CheapMansNode/Cheap-Mans-Node/Pics/3dprinting/3dprinting-02.png

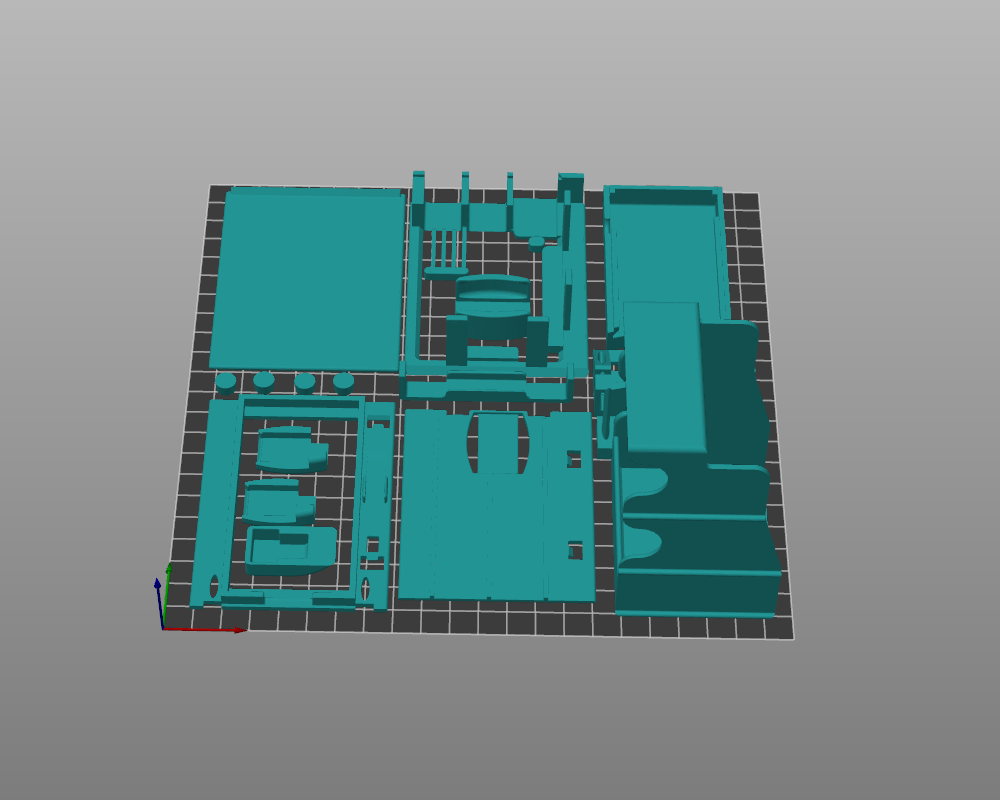
Pics/3dprinting/3dprinting-02.png
