CheapMansNode/Cheap-Mans-Node/Pics/3dprinting/3dprinting-03.png

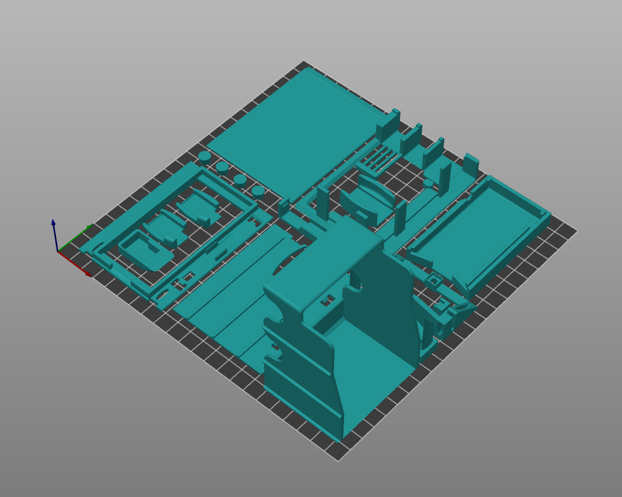
Pics/3dprinting/3dprinting-03.png
