CheapMansNode/Cheap-Mans-Node/Pics/3dprinting/3dprinting-04.png

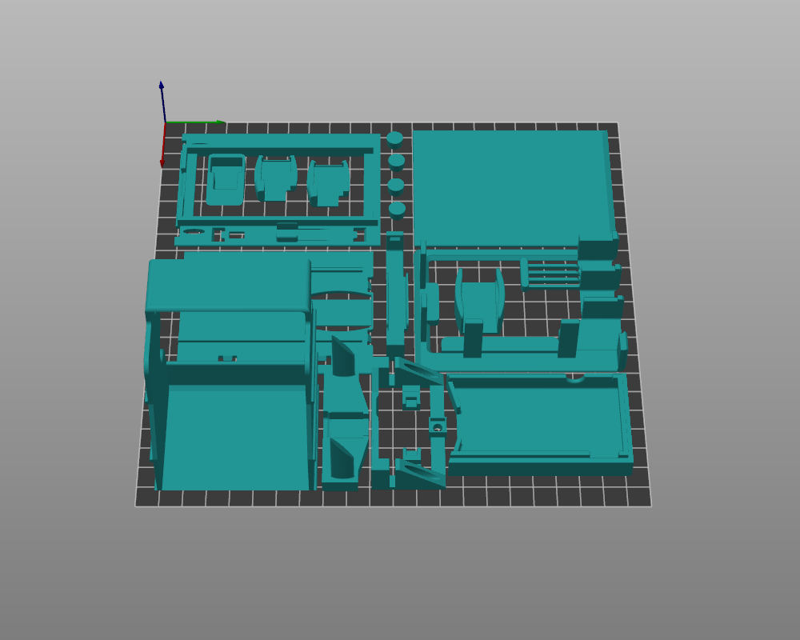
Pics/3dprinting/3dprinting-04.png
