CheapMansNode/Cheap-Mans-Node/Pics/3dprinting/3dprinting-05.png

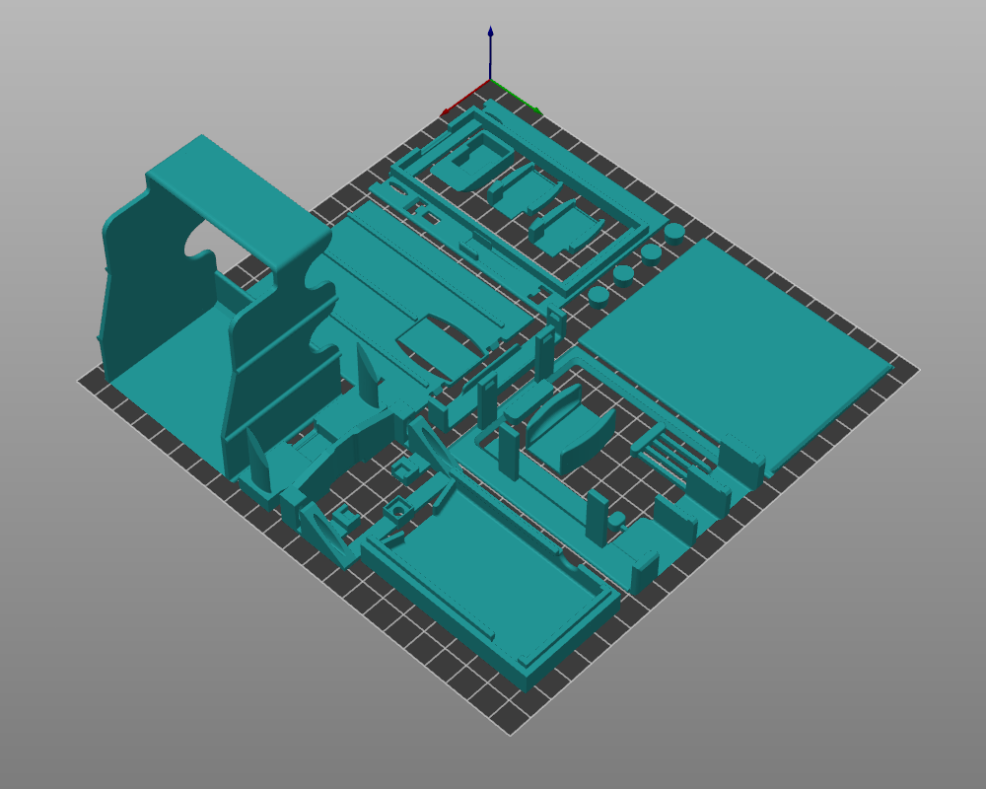
Pics/3dprinting/3dprinting-05.png
