CheapMansNode/Cheap-Mans-Node/Pics/3dprinting/3dprinting-06.png

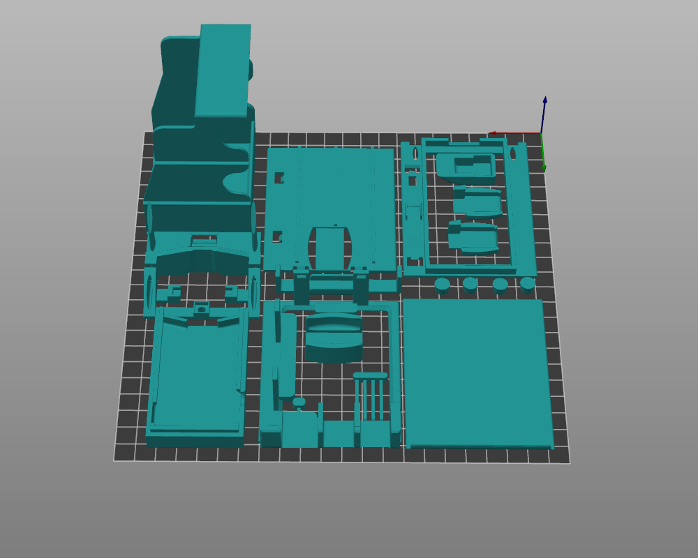
Pics/3dprinting/3dprinting-06.png
