CheapMansNode/Cheap-Mans-Node/Pics/3dprinting/3dprinting-07.png

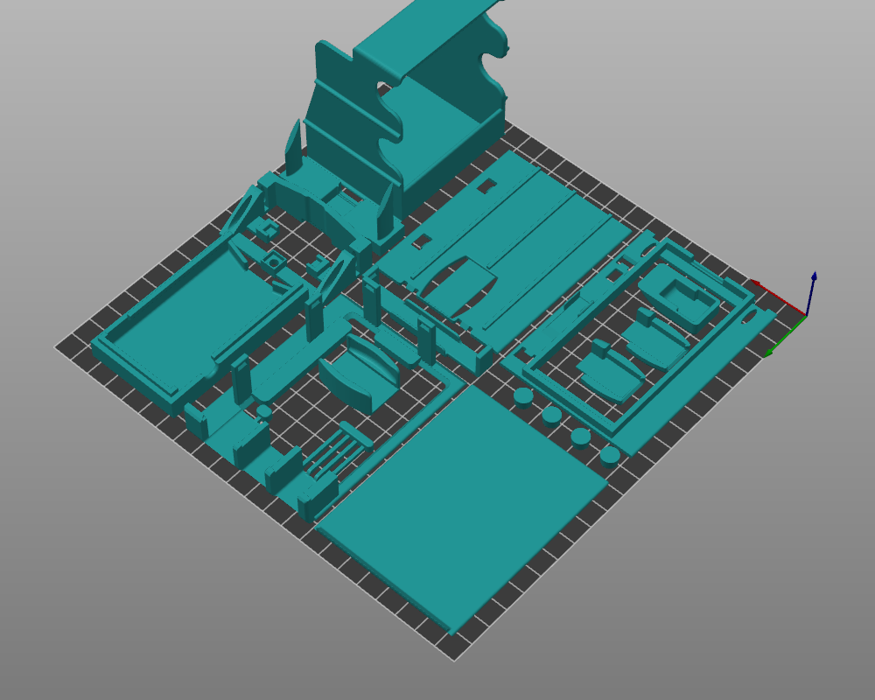
Pics/3dprinting/3dprinting-07.png
