CheapMansNode/Cheap-Mans-Node/Pics/3dprinting/3dprinting-08.png

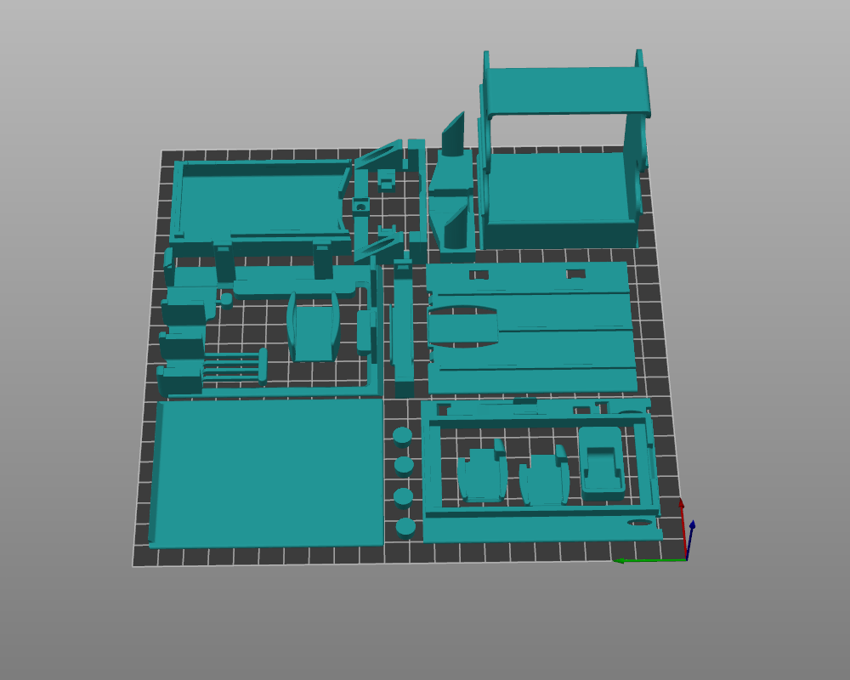
Pics/3dprinting/3dprinting-08.png
