CheapMansNode/Cheap-Mans-Node/Pics/3dprinting/3dprinting-09.png

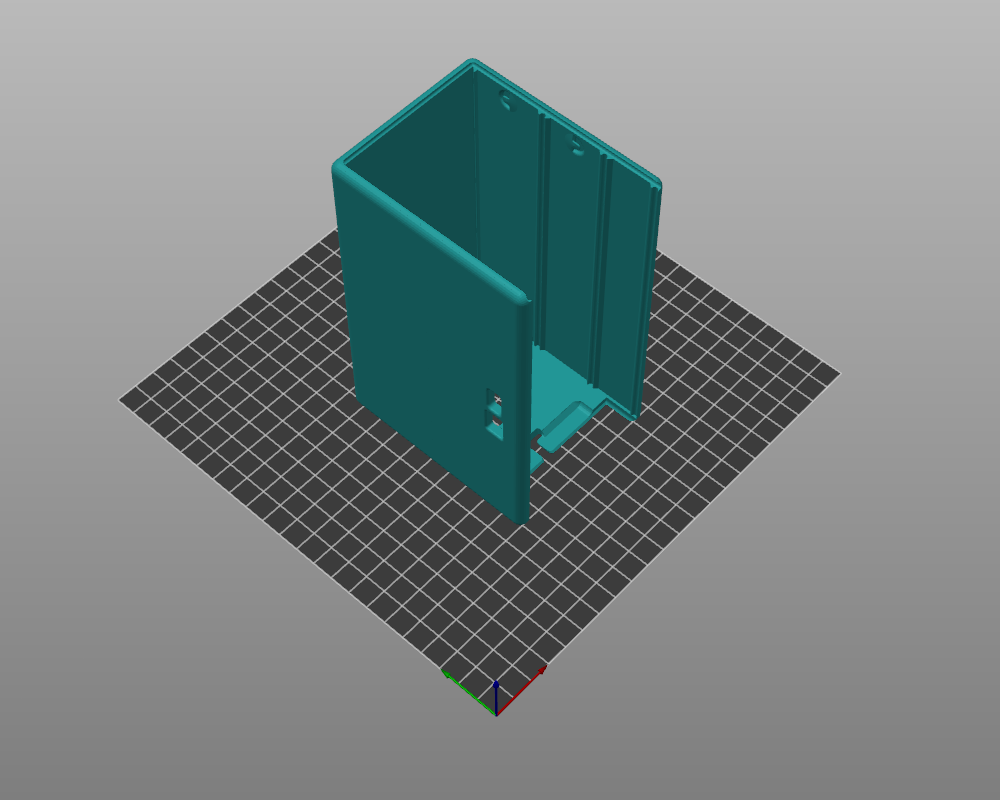
Pics/3dprinting/3dprinting-09.png
