CheapMansNode/Cheap-Mans-Node/Pics/3dprinting/3dprinting-10.png

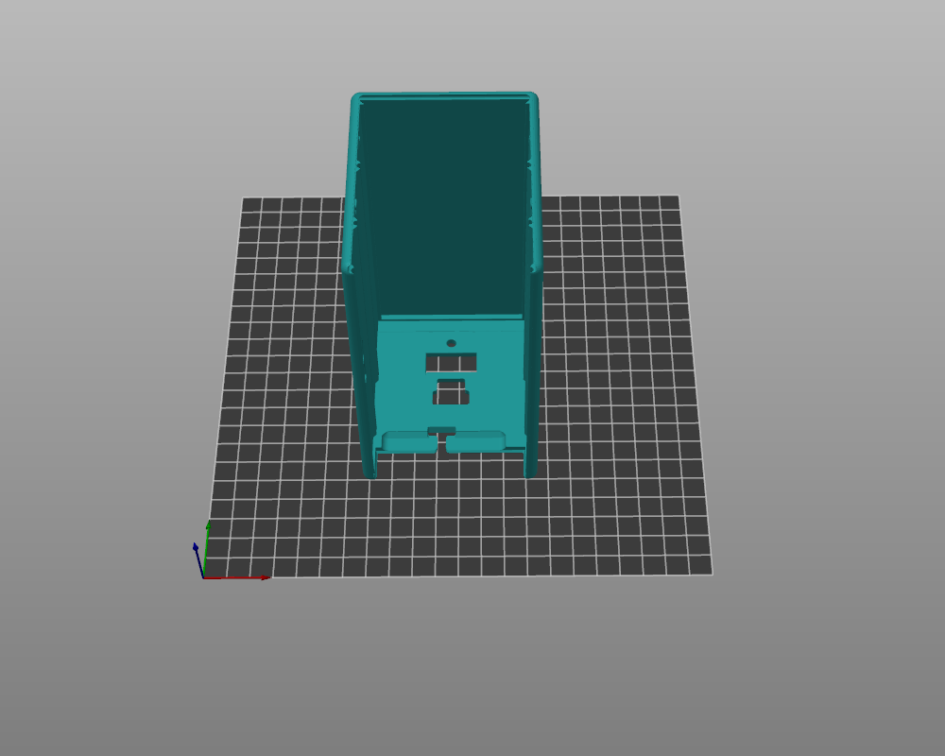
Pics/3dprinting/3dprinting-10.png
