CheapMansNode/Cheap-Mans-Node/Pics/3dprinting/3dprinting-11.png

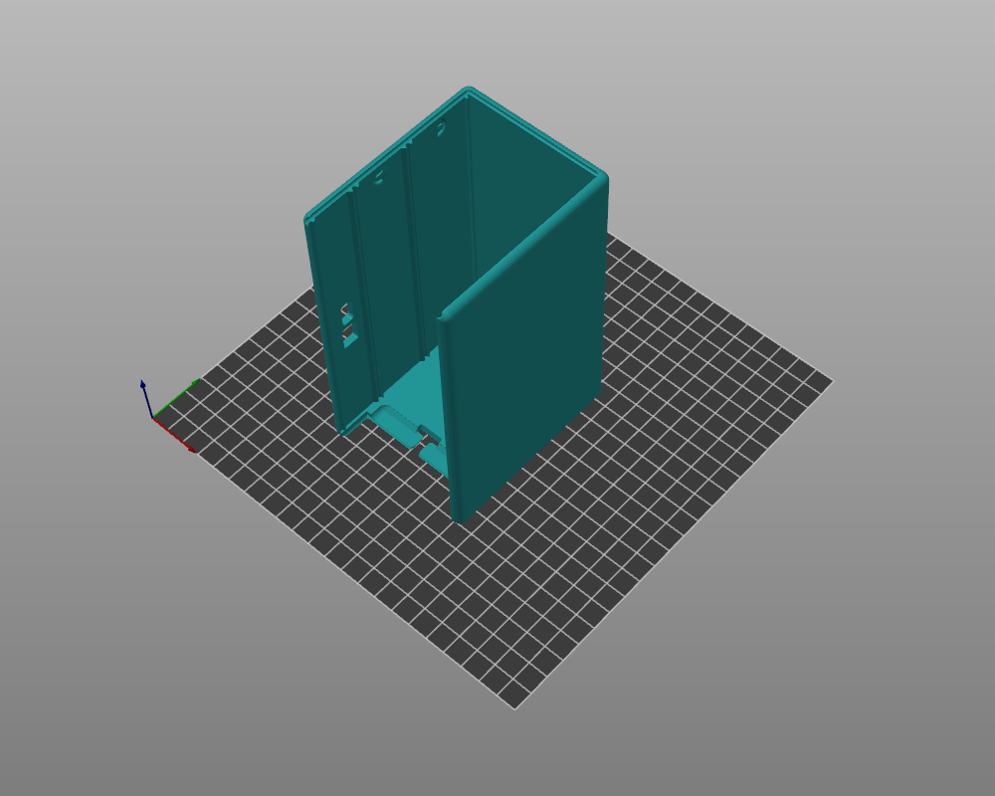
Pics/3dprinting/3dprinting-11.png
