CheapMansNode/Cheap-Mans-Node/Pics/3dprinting/3dprinting-12.png

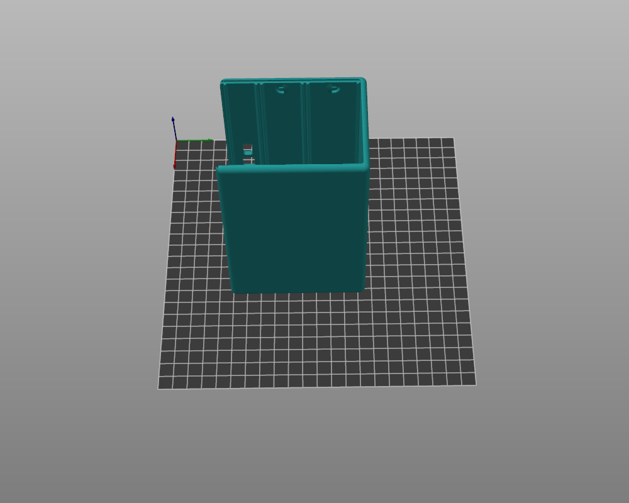
Pics/3dprinting/3dprinting-12.png
