CheapMansNode/Cheap-Mans-Node/Pics/3dprinting/3dprinting-14.png

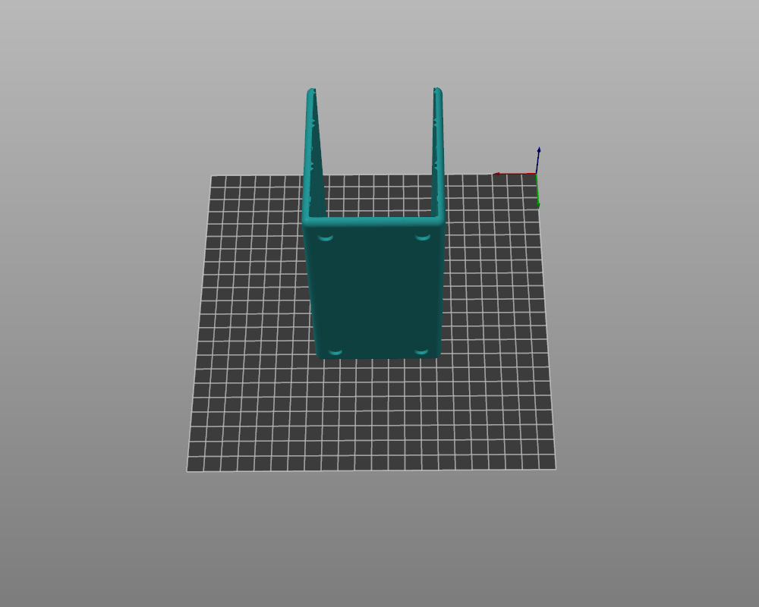
Pics/3dprinting/3dprinting-14.png
