CheapMansNode/Cheap-Mans-Node/Pics/3dprinting/3dprinting-15.png

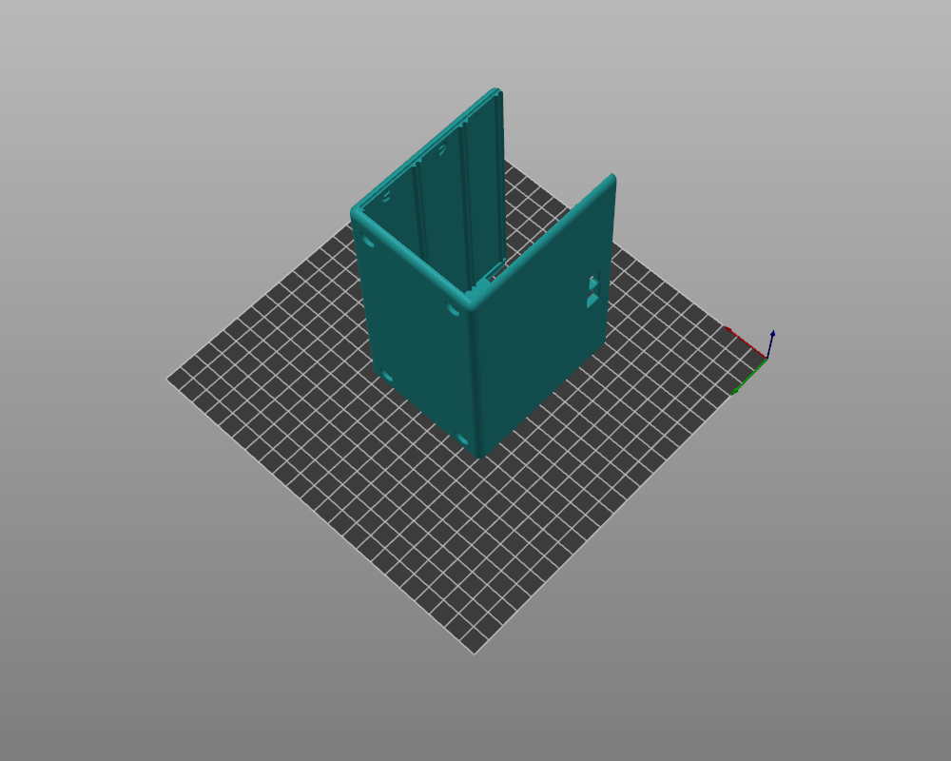
Pics/3dprinting/3dprinting-15.png
