CheapMansNode/Cheap-Mans-Node/Pics/3dprinting/3dprinting-16.png

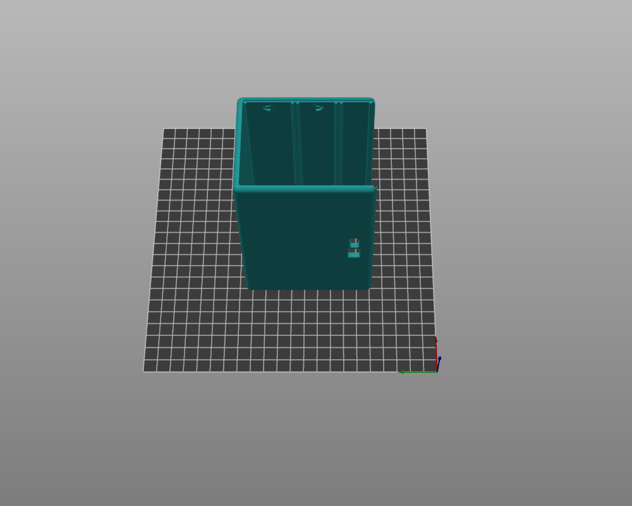
Pics/3dprinting/3dprinting-16.png
