CheapMansNode/Cheap-Mans-Node/Pics/cmn_round_image.jpg

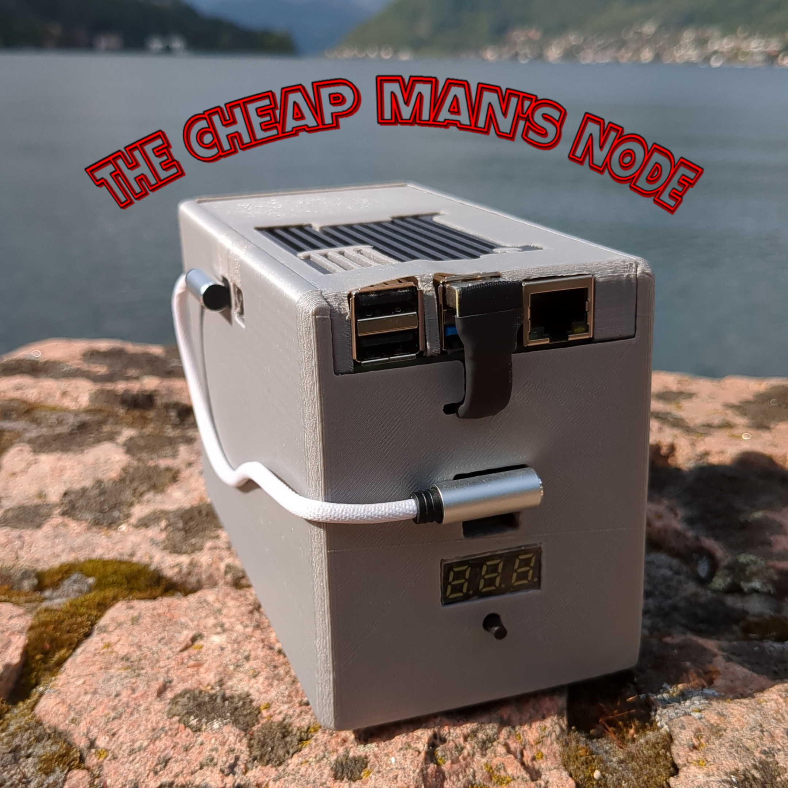
Pics/cmn_round_image.jpg
