CheapMansNode/Cheap-Mans-Node/Pics/gif_pics.gif

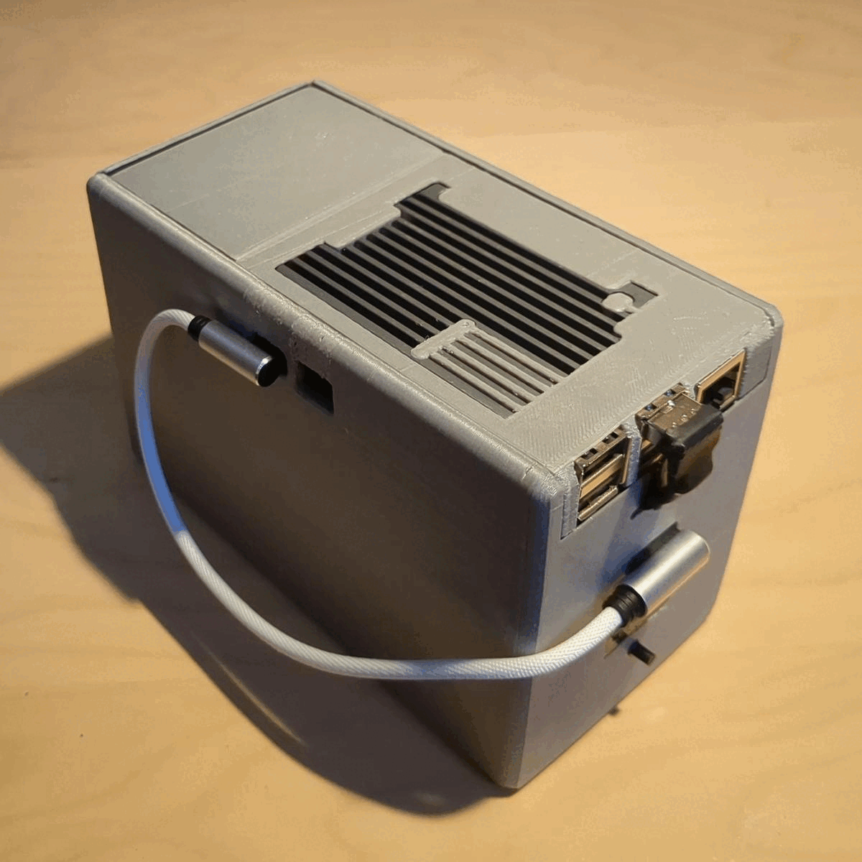
Pics/gif_pics.gif
