CheapMansNode/Cheap-Mans-Node/Pics/gif_render.gif

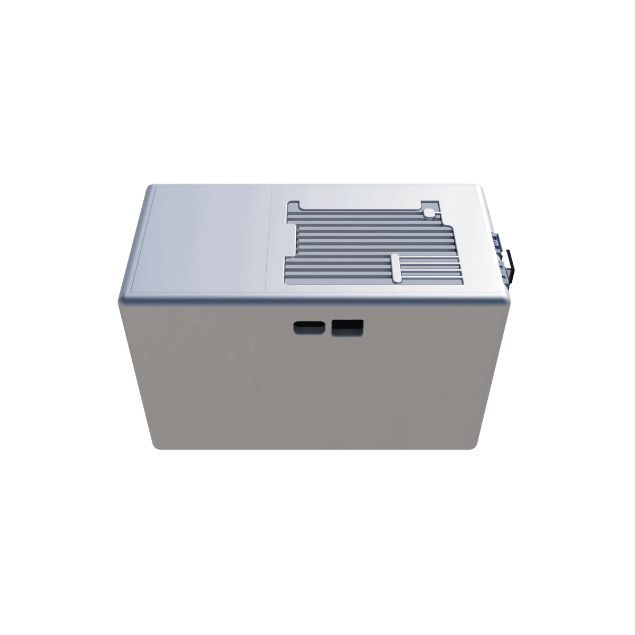
Pics/gif_render.gif
