CheapMansNode/Cheap-Mans-Node/Pics/Render/2.PNG

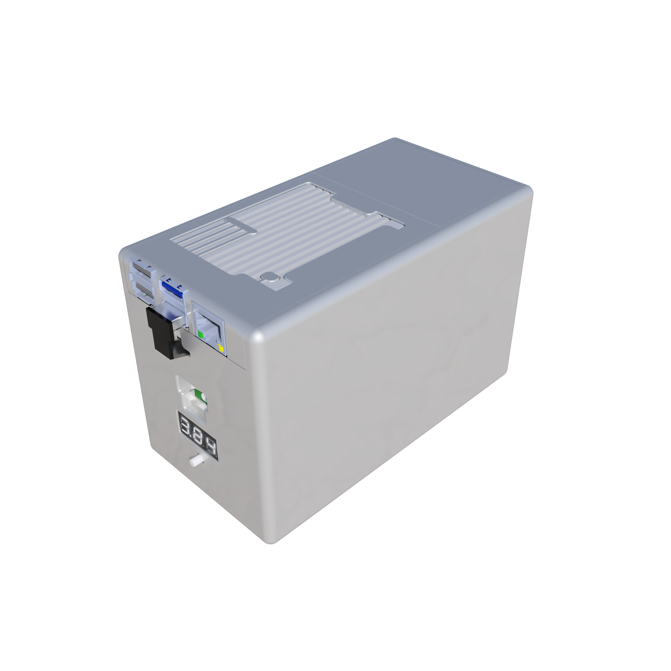
Pics/Render/2.PNG
