CheapMansNode/Cheap-Mans-Node/Pics/Render/3.PNG

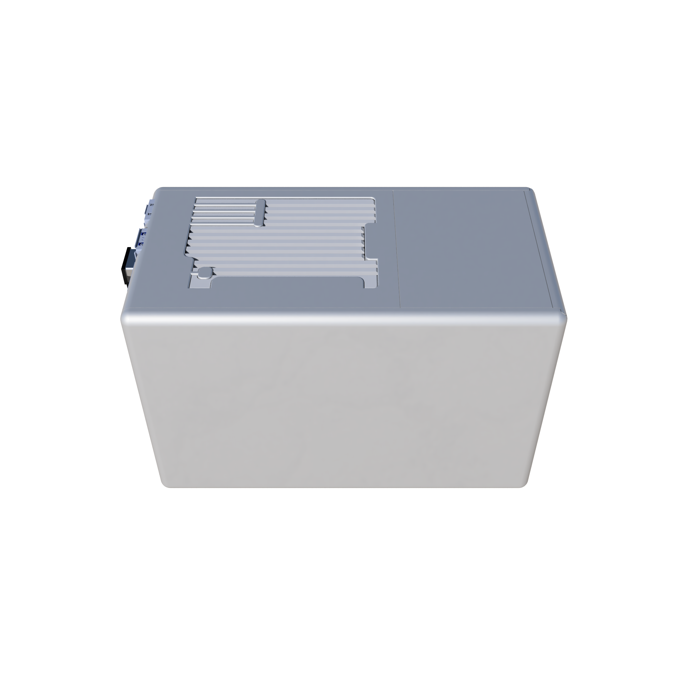
Pics/Render/3.PNG
