CheapMansNode/Cheap-Mans-Node/Pics/Render/4.PNG

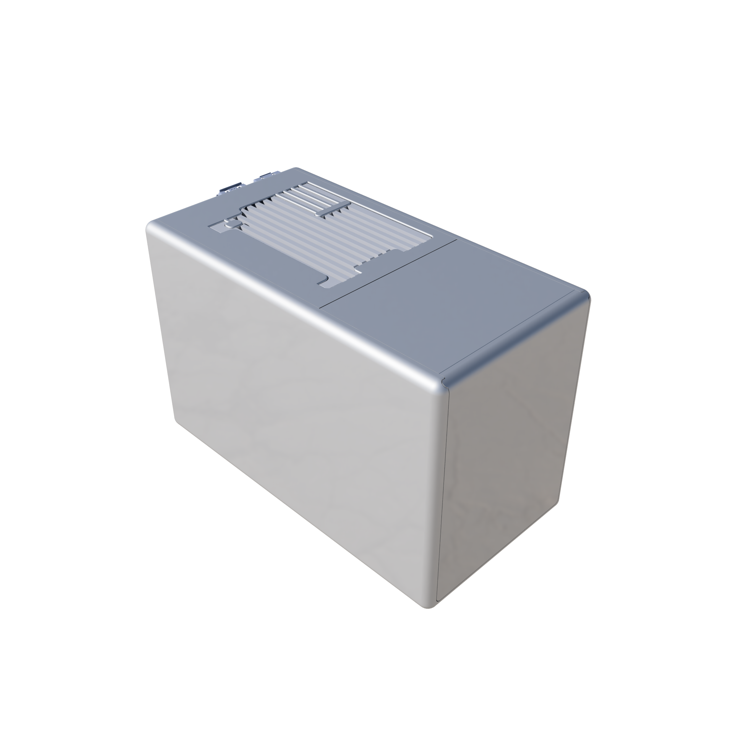
Pics/Render/4.PNG
