CheapMansNode/Cheap-Mans-Node/Pics/Render/5.PNG

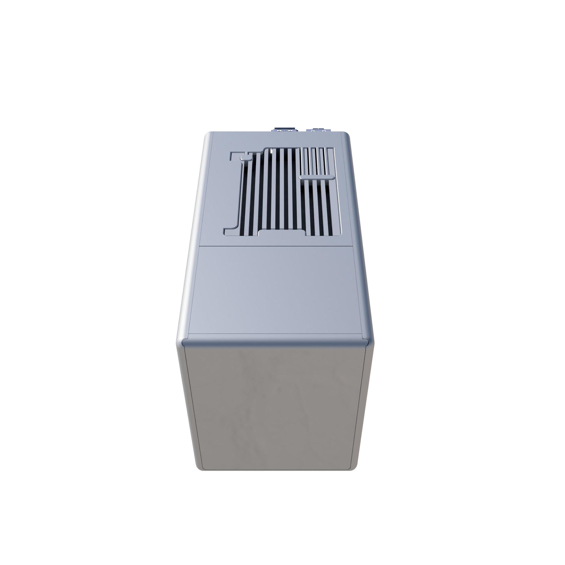
Pics/Render/5.PNG
