CheapMansNode/Cheap-Mans-Node/Pics/Render/6.png

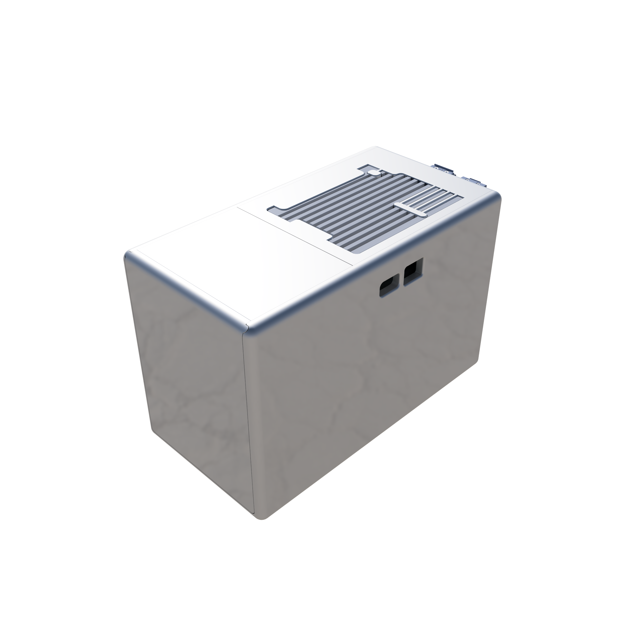
Pics/Render/6.png
