CheapMansNode/Cheap-Mans-Node/Pics/Render/8.png

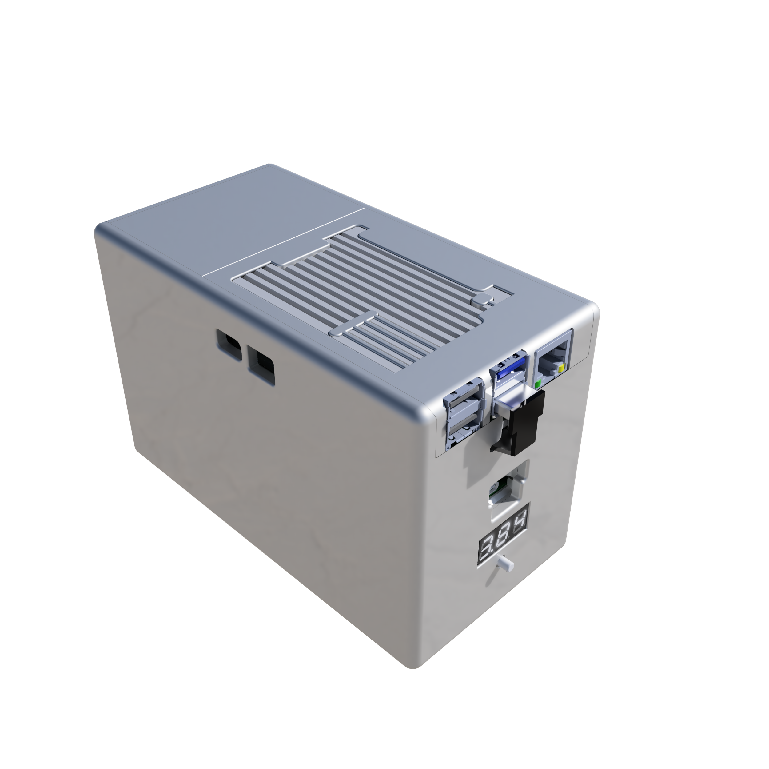
Pics/Render/8.png
