CheapMansNode/Cheap-Mans-Node/Pics/top_a_or_b.jpg

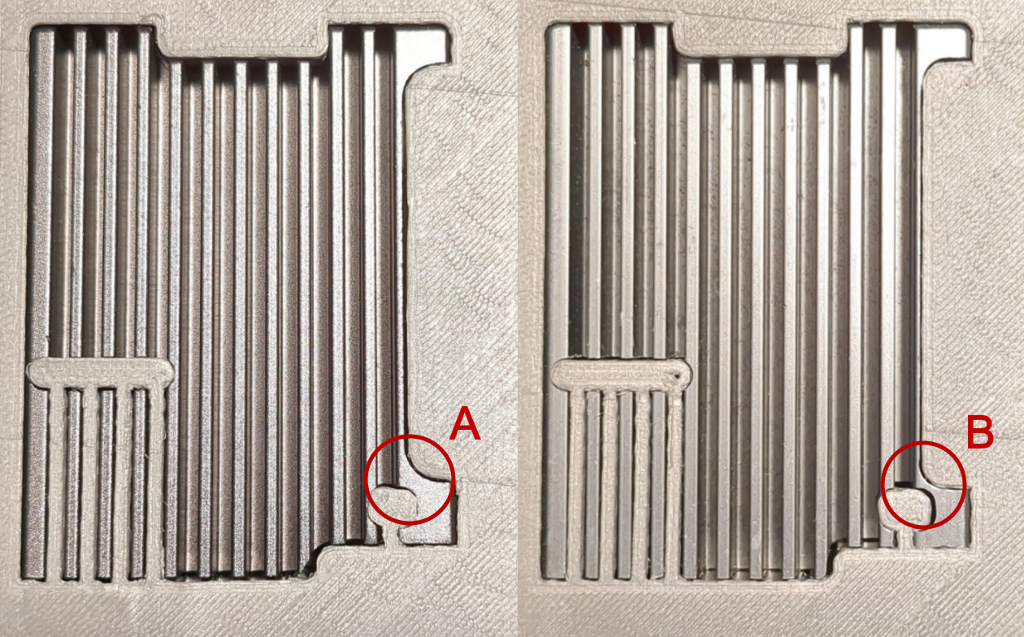
Pics/top_a_or_b.jpg
