CheapMansNode/Cheap-Mans-Node/Pics/3D Printed/1.jpg

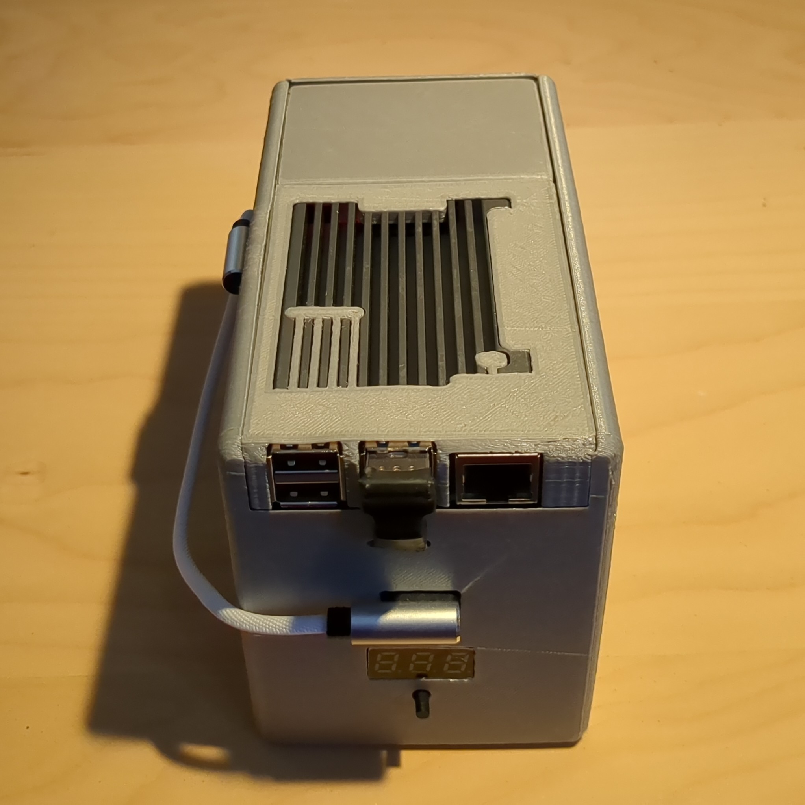
Pics/3D Printed/1.jpg
