CheapMansNode/Cheap-Mans-Node/Pics/3D Printed/2.jpg

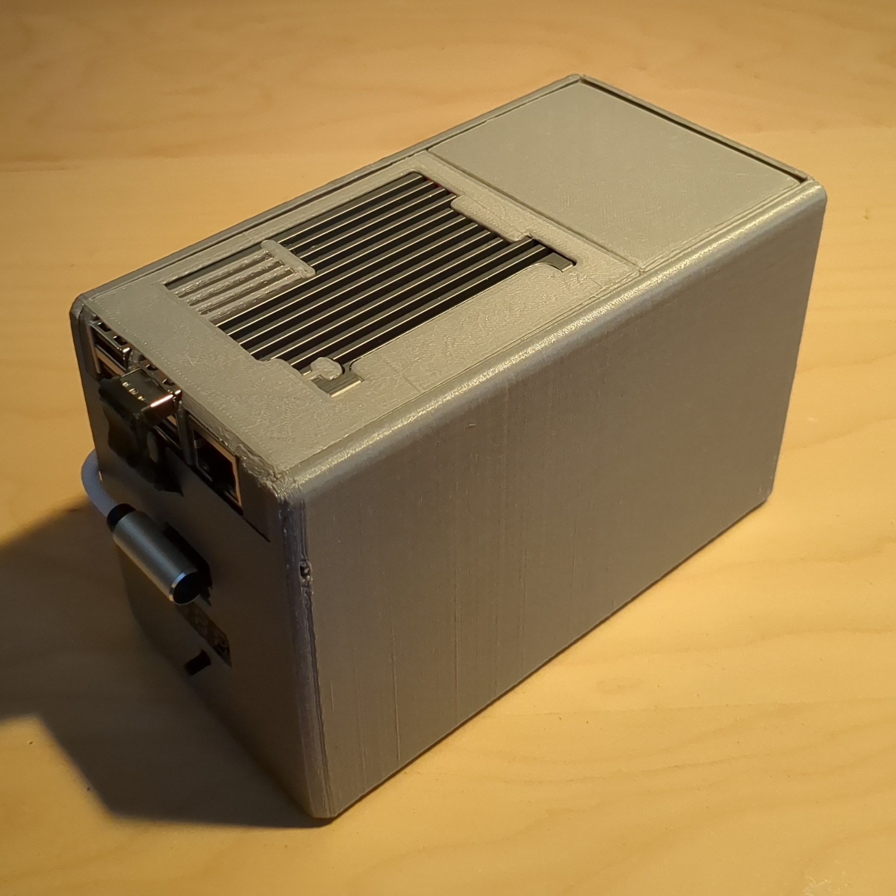
Pics/3D Printed/2.jpg
