CheapMansNode/Cheap-Mans-Node/Pics/3D Printed/6.jpg

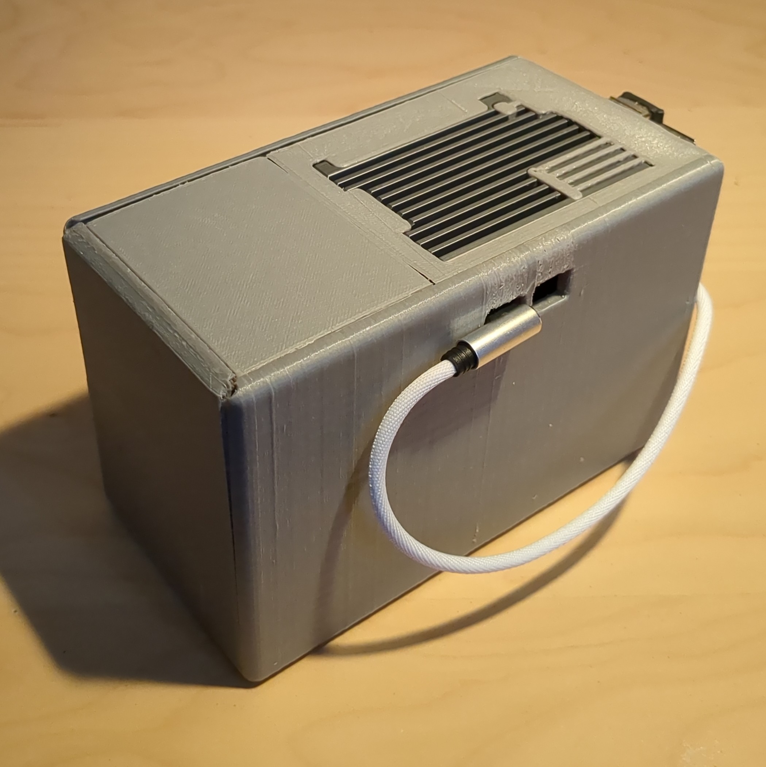
Pics/3D Printed/6.jpg
