CheapMansNode/Cheap-Mans-Node/Pics/3D Printed/front.jpg

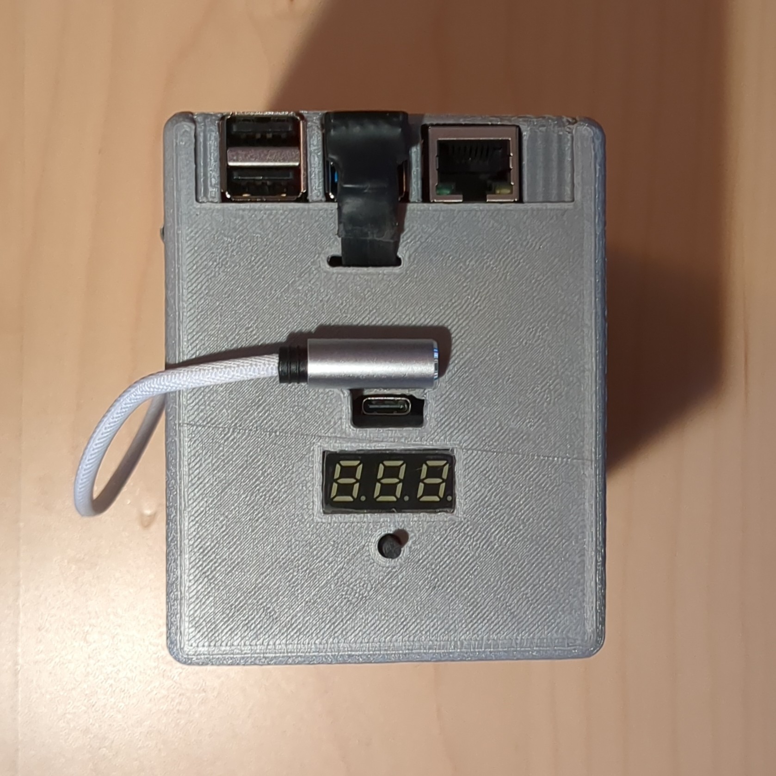
Pics/3D Printed/front.jpg
