CheapMansNode/Cheap-Mans-Node/Pics/3D Printed/top.jpg

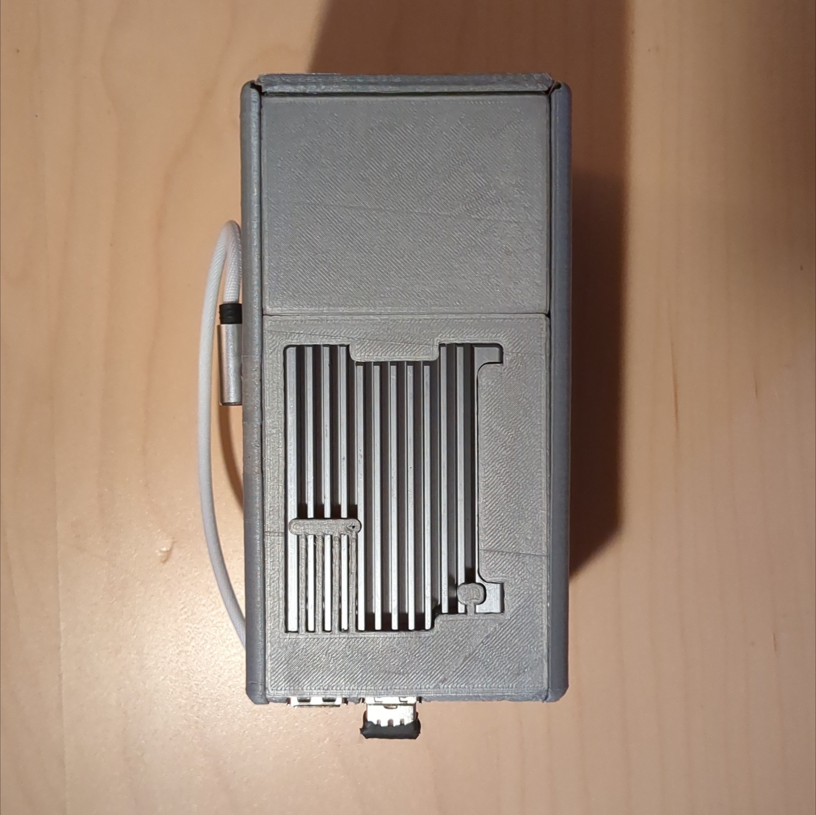
Pics/3D Printed/top.jpg
